e-dreyer/OpenEnclosure/models/fan_duct/daughter_board_mount.3mf

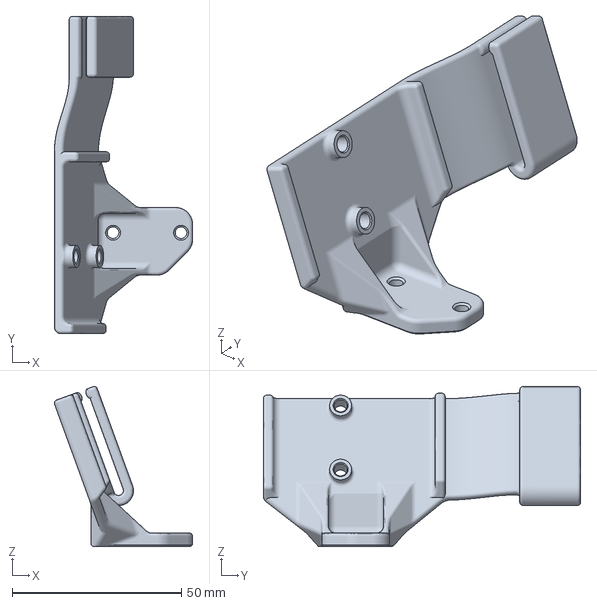
[picture p19: CAD file, 2023-11-01]
models/fan_duct/daughter_board_mount.3mf
40.8 x 93.8 x 47.3 mm
