e-dreyer/OpenEnclosure/models/honeycomb_wall/honeycomb_wall_web_cam_rail.3mf

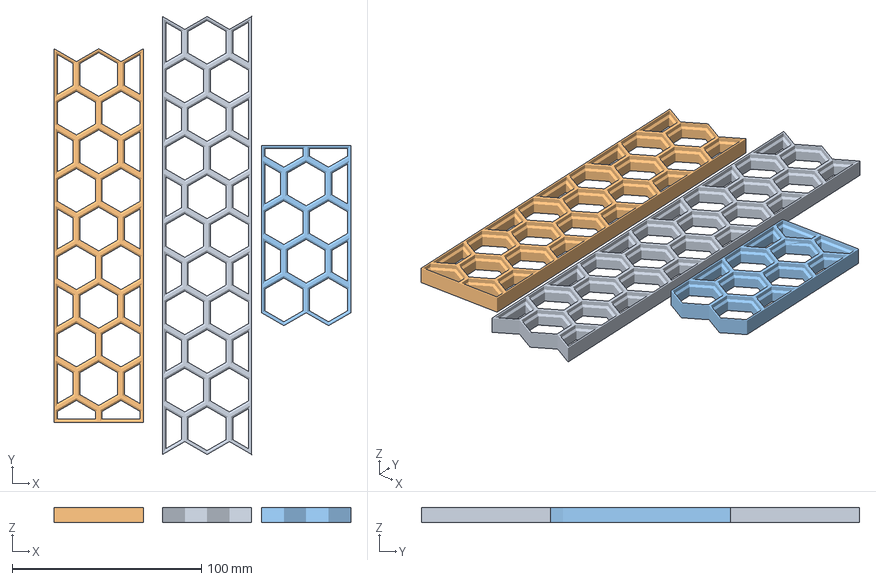
[picture p20: CAD file, 2023-11-01]
models/honeycomb_wall/honeycomb_wall_web_cam_rail.3mf
156.9 x 231.6 x 8.00 mm
honeycomb_wall_230x50_flipped
honeycomb_wall_210x50
honeycomb_wall_100x50
