e-dreyer/OpenEnclosure/models/led_bar/parametric_led_bar_v5.step

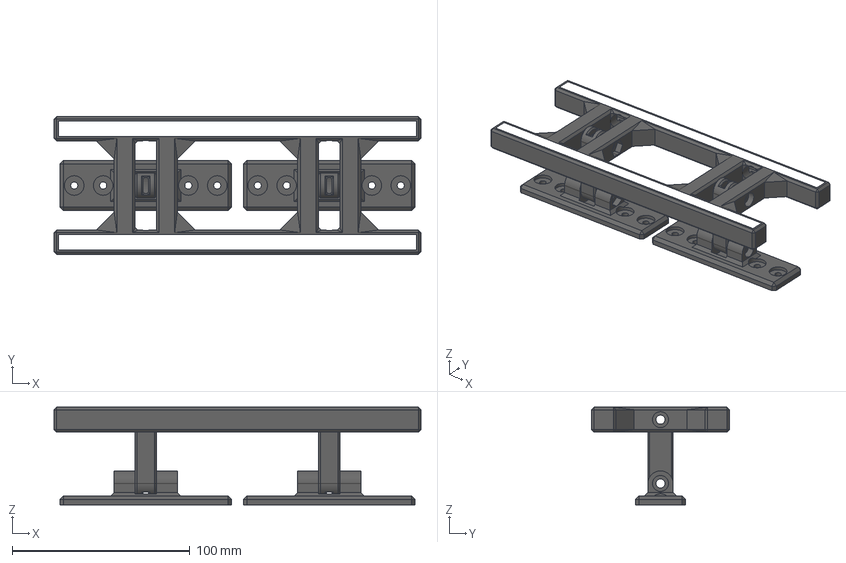
[picture p21: CAD file, 2023-11-01]
models/led_bar/parametric_led_bar_v5.step
206.3 x 77.7 x 55.0 mm
led_strip
transparent_cover
led_bar
middle_bracket
mounting_bracket
