e-dreyer/OpenEnclosure/models/pi_enclosure/pi_enclosure_bottom.stl

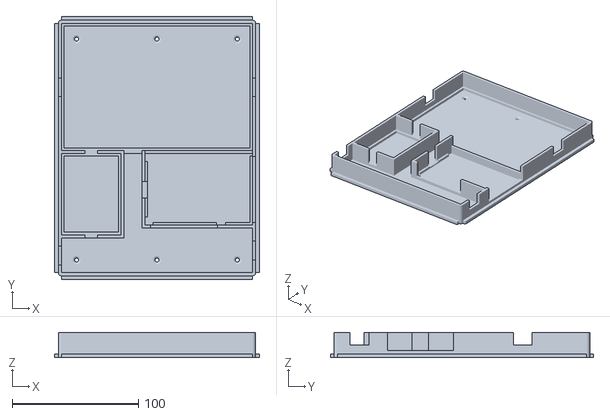
[picture p22: CAD file, 2023-11-01]
models/pi_enclosure/pi_enclosure_bottom.stl
162.3 x 208.4 x 20.0
