e-dreyer/OpenEnclosure/volumetric_flow_tests/Max volumetric speed test CR6SE.3mf

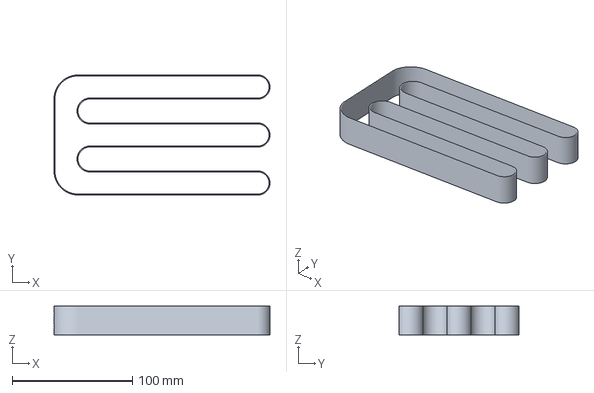
[picture p23: CAD file, 2023-11-13]
volumetric_flow_tests/Max volumetric speed test CR6SE.3mf
180.0 x 100.0 x 24.0 mm
