e-dreyer/OpenEnclosure/models/camera/focus_ring.stl

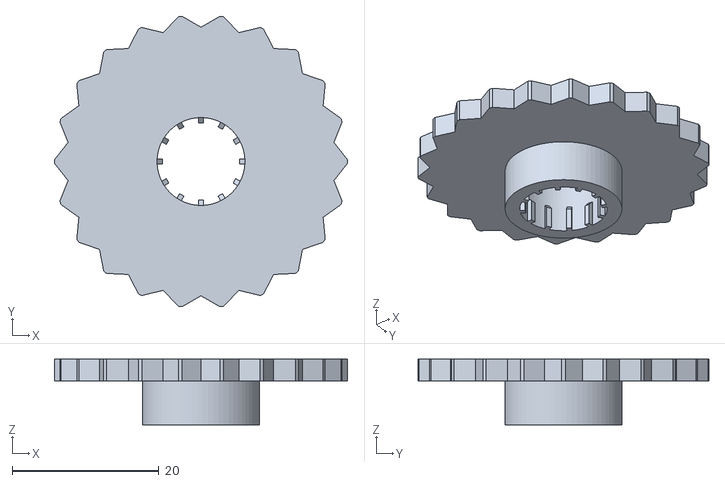
[picture p24: CAD file, 2023-11-01]
models/camera/focus_ring.stl
40.0 x 39.7 x 9.00
