e-dreyer/OpenEnclosure/models/honeycomb_wall/hook_20mm.step

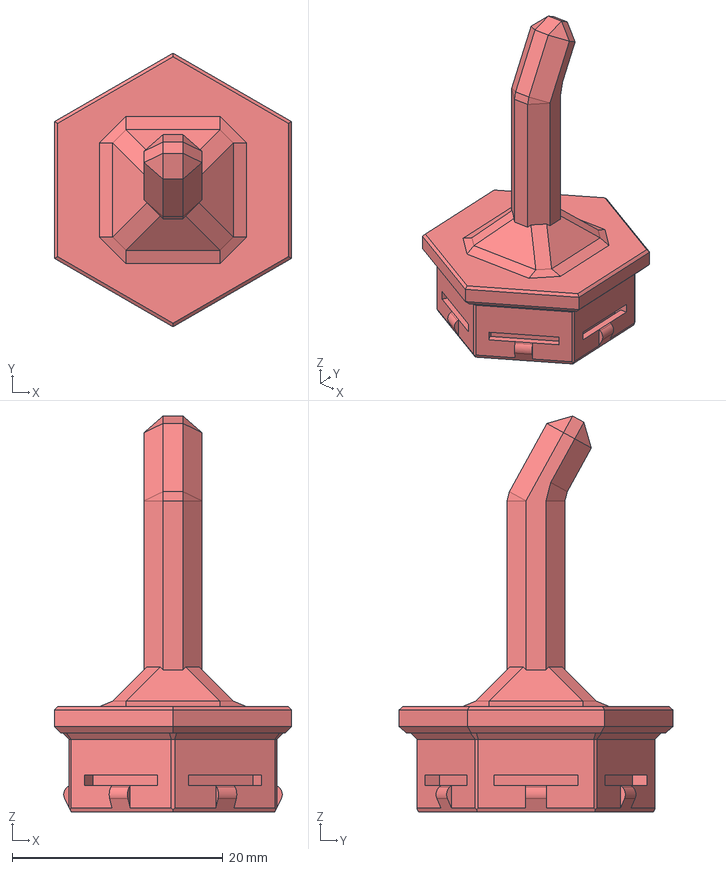
[picture p25: CAD file, 2023-11-01]
models/honeycomb_wall/hook_20mm.step
22.5 x 26.0 x 37.6 mm
