e-dreyer/OpenEnclosure/models/led_bar/transparent_cover_v5.step

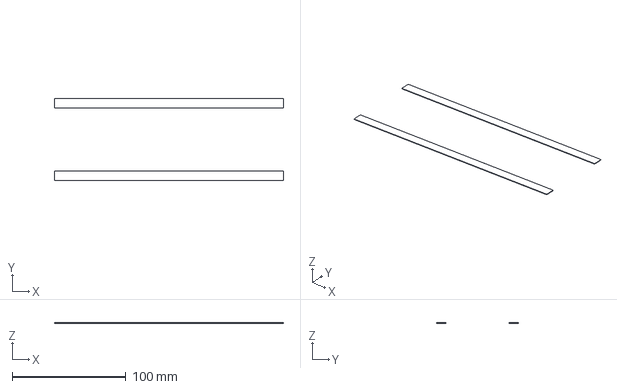
[picture p26: CAD file, 2023-11-01]
models/led_bar/transparent_cover_v5.step
201.0 x 72.3 x 0.48 mm
