e-dreyer/OpenEnclosure/models/camera/base.stl

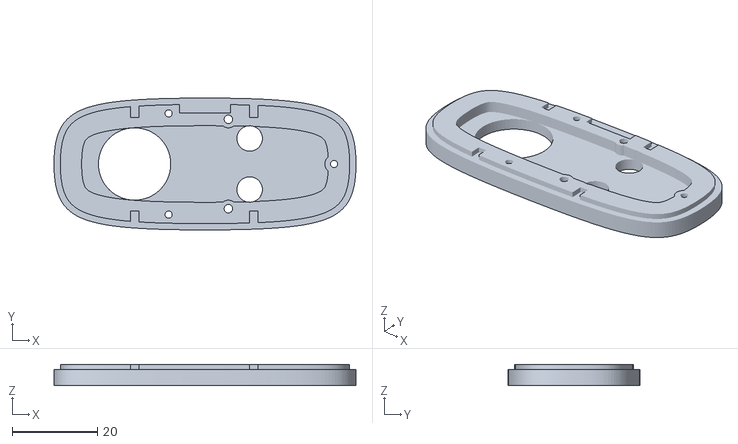
[picture p27: CAD file, 2023-11-01]
models/camera/base.stl
71.0 x 31.0 x 5.00
