e-dreyer/OpenEnclosure/models/honeycomb_wall/honeycomb_wall_40x50.3mf

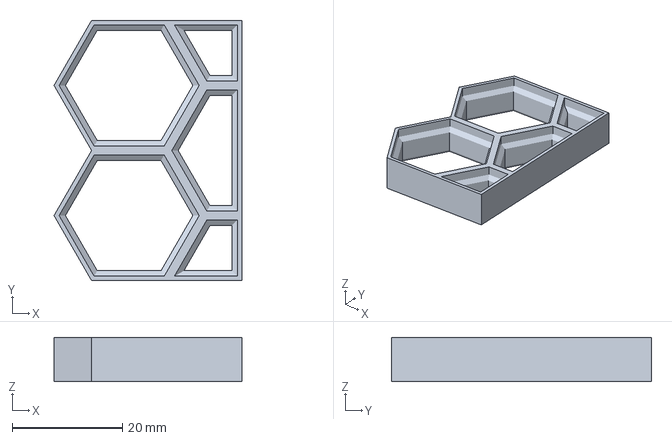
[picture p28: CAD file, 2023-11-01]
models/honeycomb_wall/honeycomb_wall_40x50.3mf
47.7 x 47.2 x 8.00 mm
