e-dreyer/OpenEnclosure/models/led_bar/middle_bracket_v5.step

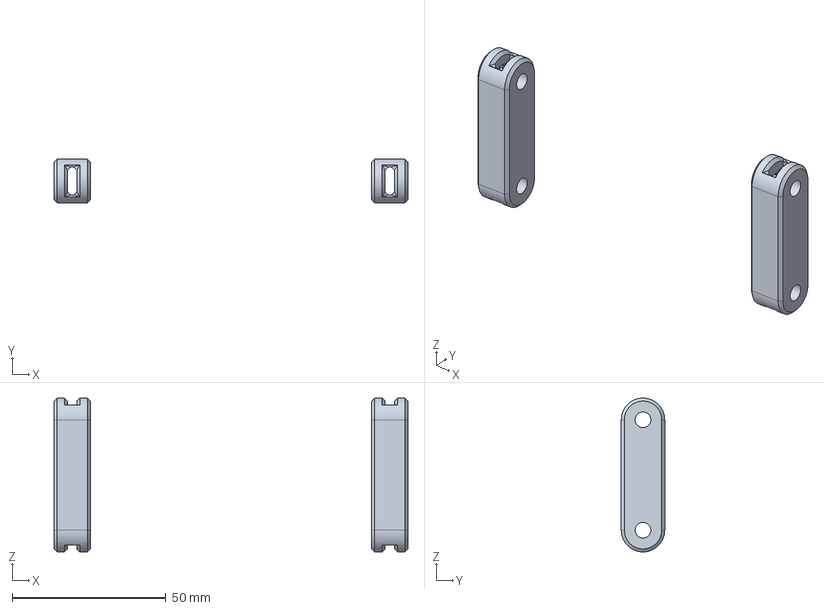
[picture p29: CAD file, 2023-11-01]
models/led_bar/middle_bracket_v5.step
115.0 x 14.1 x 50.0 mm
