e-dreyer/OpenEnclosure/models/honeycomb_wall/hook_30mm.step

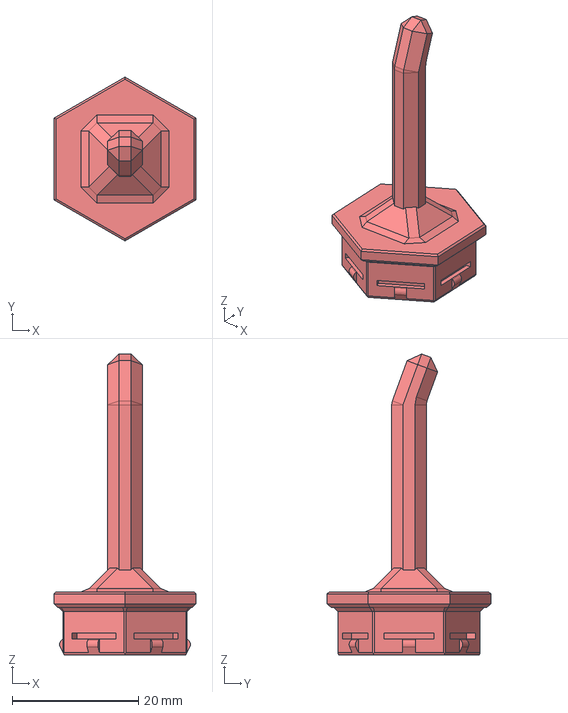
[picture p30: CAD file, 2023-11-01]
models/honeycomb_wall/hook_30mm.step
22.5 x 26.0 x 47.7 mm
