e-dreyer/OpenEnclosure/models/led_bar/mounting_bracket_v5.step

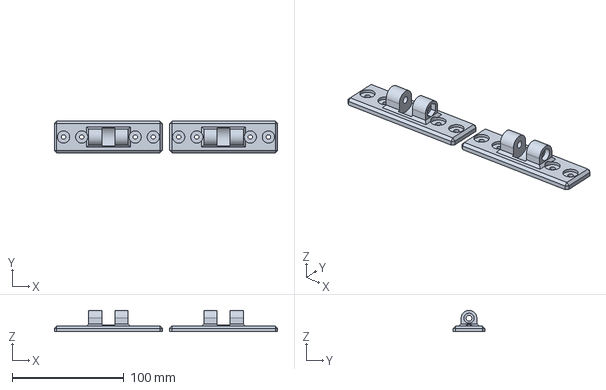
[picture p31: CAD file, 2023-11-01]
models/led_bar/mounting_bracket_v5.step
199.8 x 28.3 x 19.1 mm
