e-dreyer/OpenEnclosure/models/honeycomb_wall/honeycomb_wall_80x50_flipped.3mf

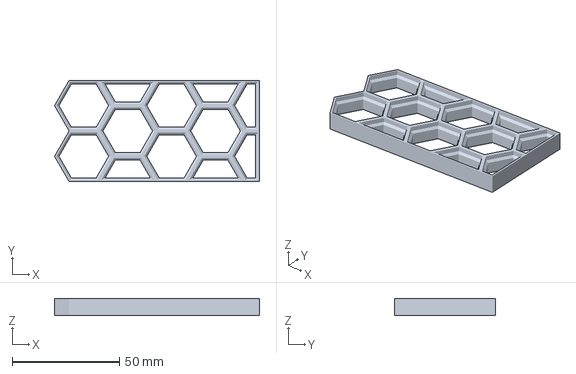
[picture p32: CAD file, 2023-11-01]
models/honeycomb_wall/honeycomb_wall_80x50_flipped.3mf
95.4 x 47.2 x 8.00 mm
