e-dreyer/OpenEnclosure/models/honeycomb_wall/insert_countersunk.3mf

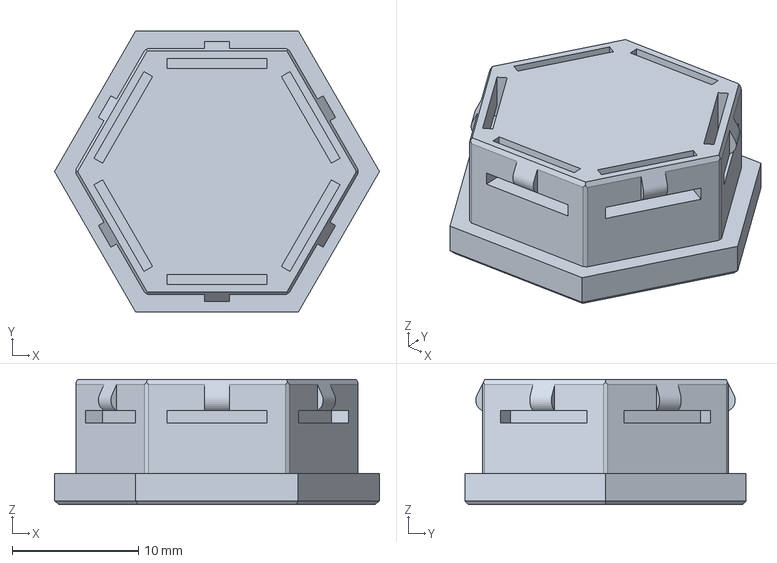
[picture p33: CAD file, 2023-11-01]
models/honeycomb_wall/insert_countersunk.3mf
25.8 x 22.3 x 9.92 mm
