e-dreyer/OpenEnclosure/models/honeycomb_wall/wall_230x230.3mf

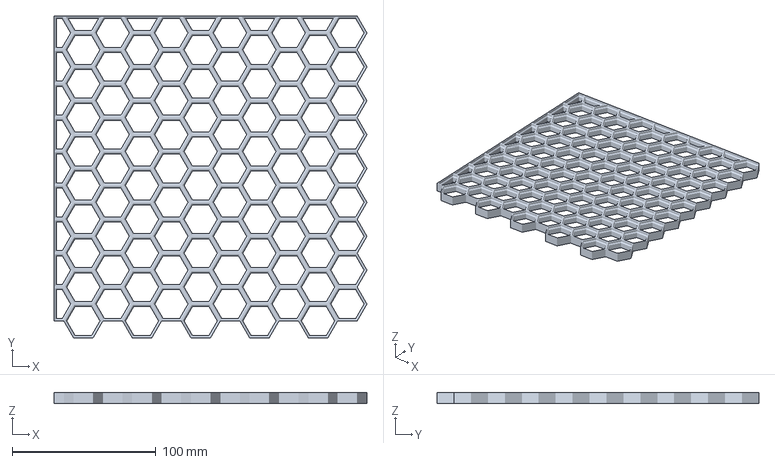
[picture p34: CAD file, 2023-11-01]
models/honeycomb_wall/wall_230x230.3mf
218.0 x 224.2 x 8.00 mm
