e-dreyer/OpenEnclosure/models/honeycomb_wall/hook_15mm.step

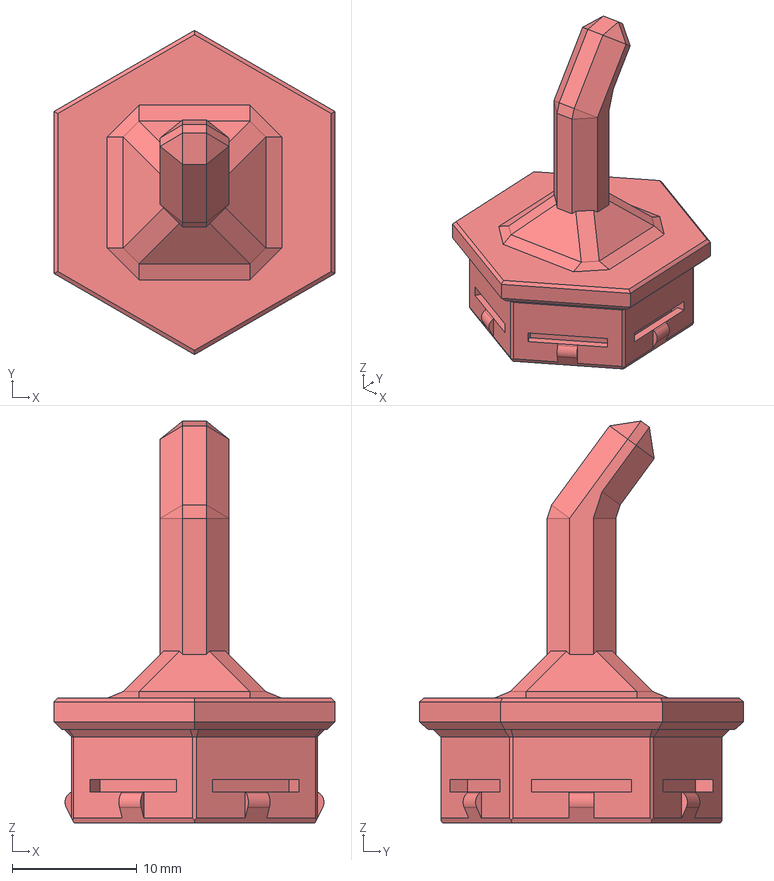
[picture p35: CAD file, 2023-11-01]
models/honeycomb_wall/hook_15mm.step
22.5 x 26.0 x 32.2 mm
