e-dreyer/OpenEnclosure/models/honeycomb_wall/hook_25mm.step

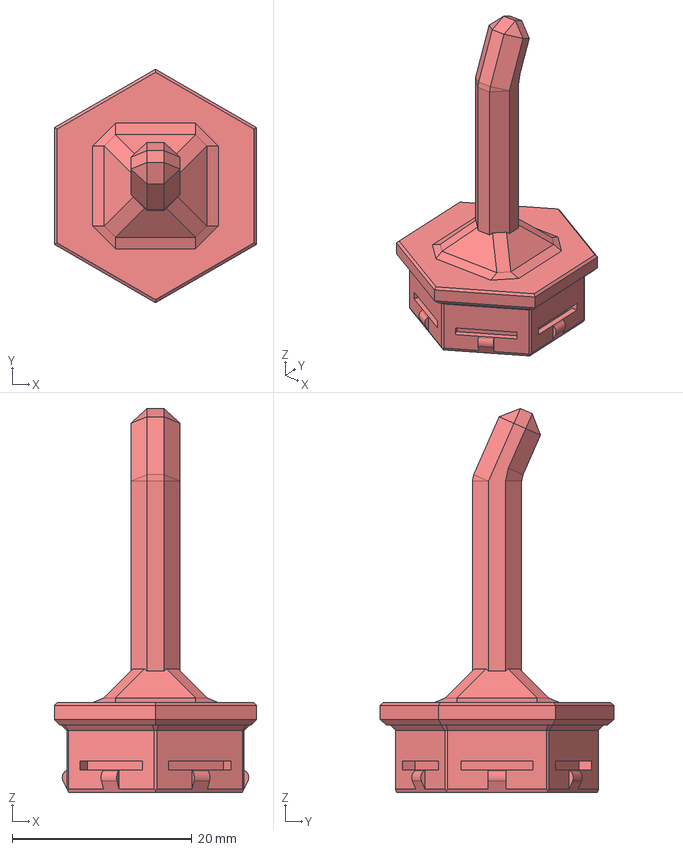
[picture p36: CAD file, 2023-11-01]
models/honeycomb_wall/hook_25mm.step
22.5 x 26.0 x 42.7 mm
