e-dreyer/OpenEnclosure/models/honeycomb_wall/honeycomb_wall_230x50_flipped.3mf

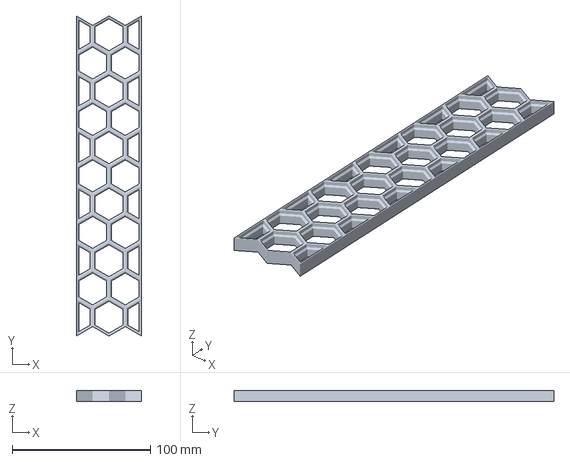
[picture p37: CAD file, 2023-11-01]
models/honeycomb_wall/honeycomb_wall_230x50_flipped.3mf
47.2 x 231.6 x 8.00 mm
