e-dreyer/OpenEnclosure/models/honeycomb_wall/honeycomb_wall_120x50.3mf

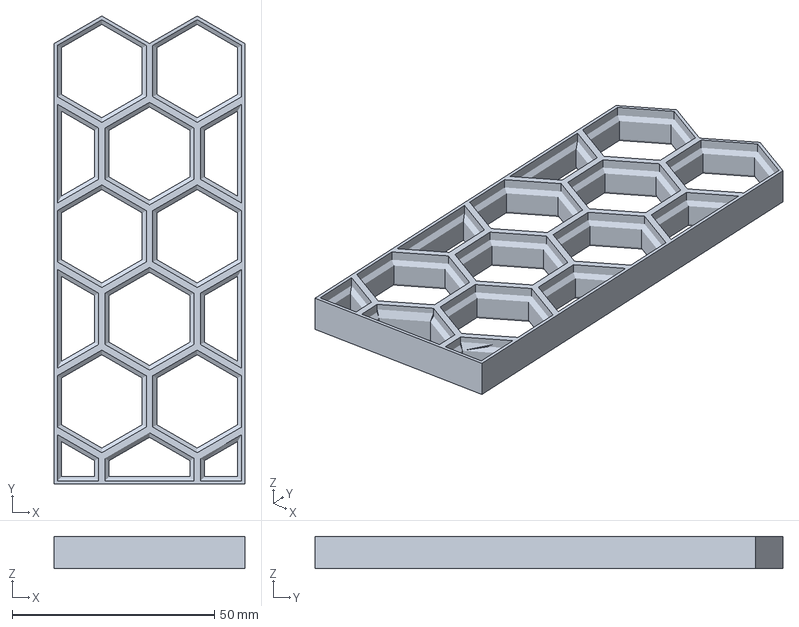
[picture p38: CAD file, 2023-11-01]
models/honeycomb_wall/honeycomb_wall_120x50.3mf
47.2 x 115.8 x 8.00 mm
