e-dreyer/OpenEnclosure/models/honeycomb_wall/honeycomb_wall_60x50.3mf

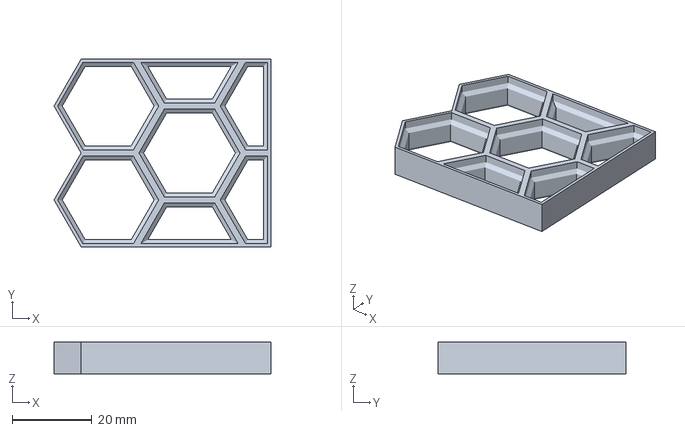
[picture p39: CAD file, 2023-11-01]
models/honeycomb_wall/honeycomb_wall_60x50.3mf
68.1 x 47.2 x 8.00 mm
