e-dreyer/OpenEnclosure/models/honeycomb_wall/honeycomb_wall_210x50.3mf

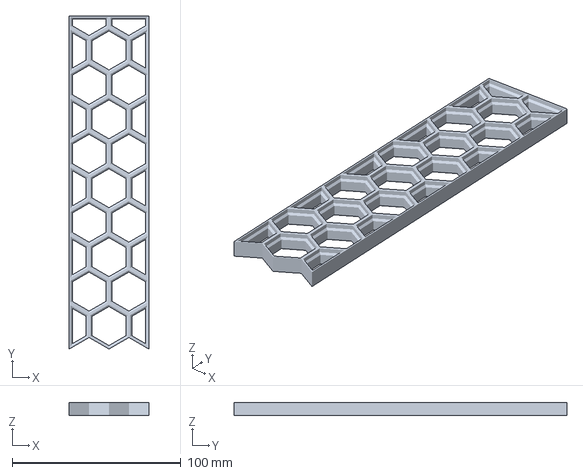
[picture p40: CAD file, 2023-11-01]
models/honeycomb_wall/honeycomb_wall_210x50.3mf
47.2 x 197.6 x 8.00 mm
