e-dreyer/OpenEnclosure/models/honeycomb_wall/cover_contersunk.3mf

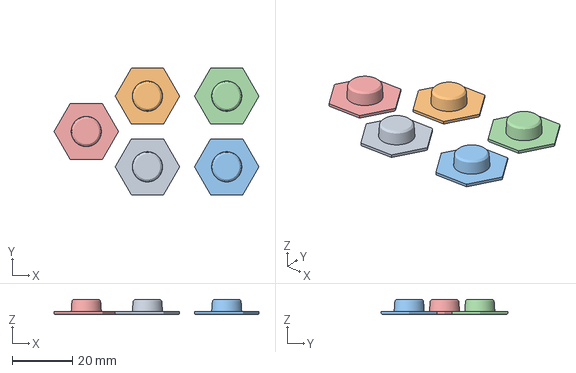
[picture p41: CAD file, 2023-11-01]
models/honeycomb_wall/cover_contersunk.3mf
67.8 x 41.9 x 5.00 mm
