e-dreyer/OpenEnclosure/models/honeycomb_wall/hook_10mm.step

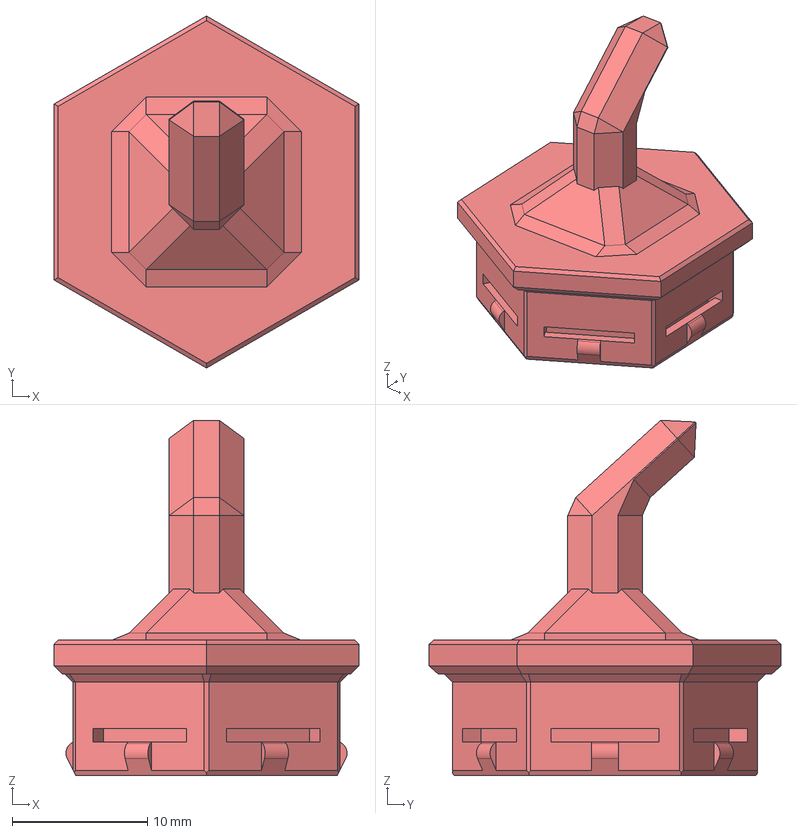
[picture p42: CAD file, 2023-11-01]
models/honeycomb_wall/hook_10mm.step
22.5 x 26.0 x 26.2 mm
