e-dreyer/OpenEnclosure/models/honeycomb_wall/hook.step

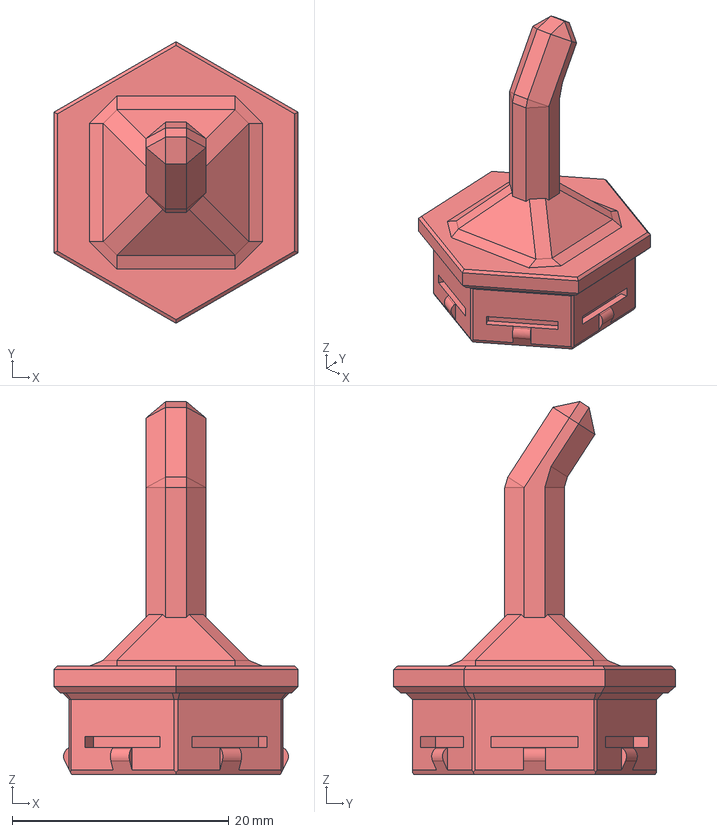
[picture p43: CAD file, 2023-11-01]
models/honeycomb_wall/hook.step
22.5 x 26.0 x 34.4 mm
